Sneftel/gull/frame/rib.scad

// The left-right-perpendicular-ish rib shape, which extends between the two spines on a side and
// supports a fingerboard. Also potentially includes the body of the thumb cluster. 

include <util.scad>
include <params.scad>

// PARAMETERS SPECIFIC TO THIS ASSEMBLY

// The height of the lowest point of the top side of the fingerboard (the fingerboard PCB will go as low as this)
FINGERBOARD_CENTER_HEIGHT = 35;

// The thickness of the fingerboard body
RIB_THICKNESS = 20;

FORWARD_STABILIZER_LOC = 30;

STABILIZER_SEAT_ANGLE = 10;

STABILIZER_SEAT_EXTRA_WIDTH = 1;

LEG_SLOT_DEPTH = 2;
LEG_SLOT_WIDTH = 2;

module LegSlot()
{
    EXTRA = 1;

    pn_neg() {
        translate([-LEG_SLOT_WIDTH/2, -LEG_SLOT_DEPTH, 0])
            square([LEG_SLOT_DEPTH,LEG_SLOT_WIDTH+EXTRA], center=false);
    }
}

module CableSlot()
{
    EXTRA = 1;
    LARGE = 100;
    translate([0, -LEG_SLOT_DEPTH])
        square([LARGE,LEG_SLOT_DEPTH+EXTRA], center=false);
}

module RearwardStabilizerSlot(extraWidth=STABILIZER_SEAT_EXTRA_WIDTH)
{
    EXTRA = 1;
    WIDTH = THICKNESS + extraWidth;

    INNER_DEPTH = STABILIZER_HEIGHT + THICKNESS * tan(STABILIZER_SEAT_ANGLE);
    OUTER_DEPTH = STABILIZER_HEIGHT - extraWidth * tan(STABILIZER_SEAT_ANGLE);

    pn_neg() {
        polygon(points = [
            [-WIDTH + THICKNESS/2, -OUTER_DEPTH],
            [THICKNESS/2, -INNER_DEPTH],
            [THICKNESS/2, EXTRA],
            [-WIDTH + THICKNESS/2, EXTRA]]);
    }

    pn_anchor("stabilizer") children();
}

module ForwardStabilizerSlot()
{
    scale([-1,1,1]) RearwardStabilizerSlot(extraWidth=10) children();
}

module OnArc(radius, x)
{
    RotZ(angleFromLen(radius, x)) translate([0,-radius,0])
        children();
}

module FingerboardPlatform(minorRadius, withTC)
{
    // The length of the rib's fingerboard platform forward of the center of the middle bolt hole
    RIB_FORWARD_EXTENT = 30 + THICKNESS/2 + STABILIZER_SEAT_EXTRA_WIDTH;

    // The length of the rib's fingerboard platform forward of the center of the middle bolt hole
    RIB_REARWARD_EXTENT = FINGERBOARD_REARWARD_EXTENT;


    TOTAL_ANGLE = angleFromLen(minorRadius, RIB_FORWARD_EXTENT+RIB_REARWARD_EXTENT);
    ANGLE_BIAS = angleFromLen(minorRadius, (RIB_FORWARD_EXTENT-RIB_REARWARD_EXTENT)/2);
    
    RotZ(ANGLE_BIAS)
    pn_pos()
        CocktailSausage(minorRadius, TOTAL_ANGLE, RIB_THICKNESS);
        
    OnArc(minorRadius, -20) FingerboardTSlot();
    OnArc(minorRadius, -10) LegSlot();
    OnArc(minorRadius, 0) FingerboardTSlot();
    OnArc(minorRadius, 10) LegSlot();
    OnArc(minorRadius, 20) FingerboardTSlot();

    OnArc(minorRadius, -30) RearwardStabilizerSlot() children();
    OnArc(minorRadius, 30) ForwardStabilizerSlot() children();
    OnArc(minorRadius, 0) pn_anchor("pcb") children();

    OnArc(minorRadius+15, 32+THICKNESS) CableGuide();

    if(withTC) {
        OnArc(minorRadius, -RIB_REARWARD_EXTENT+6) translate([0,-TC_DOWNWARD_SHIFT]) RotZ(-TC_ELEVATION_ANGLE)
        {
            pn_pos() Rect(4*TC_INTERCONNECT_OFFSET, 20, ANCHOR_RT, extraX=5);
            translate([-4*TC_INTERCONNECT_OFFSET,0]) scale([1,-1,1]) Interconnect("TC", offsetLength=TC_INTERCONNECT_OFFSET, horizontalKeepout=0) children();
        }

        //OnArc(minorRadius+12, -40-THICKNESS) RotZ(90) CableGuide();
    }
}

module Supports(shift, minorRadius)
{
    FINGERBOARD_MAJOR_RADIUS = minorRadius + RIB_THICKNESS;
    EXTRA=1;
    LARGE=100;

    pn_pos() {
        difference() {
            Rect(SPINES_OUTER_SPACING, LARGE, ANCHOR_CB);
            translate([shift, minorRadius+FINGERBOARD_CENTER_HEIGHT])
                circle(r=FINGERBOARD_MAJOR_RADIUS-EXTRA);
        }
    }

    translate([SPINES_OUTER_SPACING/2,0]) RotZ(90) Interconnect("foo", SPINE_RIB_INTERCONNECT_OFFSET);
    scale([-1,1,1]) translate([SPINES_OUTER_SPACING/2,0]) RotZ(90) Interconnect("foo", SPINE_RIB_INTERCONNECT_OFFSET);
}

module Rib(shift, minorRadius, cantAngle, withTC)
{
    Supports(shift, minorRadius) children();

    translate([shift,minorRadius+FINGERBOARD_CENTER_HEIGHT]) RotZ(cantAngle)
        FingerboardPlatform(minorRadius, withTC) children();
}


module Rib_Anchored(shift, minorRadius, cantAngle, withTC)
{
    RotZ(90)
    translate([-SPINES_OUTER_SPACING/2+THICKNESS/2, -2*SPINE_RIB_INTERCONNECT_OFFSET])
        Rib(shift, minorRadius, cantAngle, withTC) children();
}

Dekerf() pn_top() Rib_Anchored(RIB_A_SHIFT, RIB_A_RADIUS, RIB_A_PITCH, true);
