Sneftel/gull/frame/rib_c.scad

// The outer-most ribs.

include <params.scad>
use <rib.scad>

module Rib_C()
{
	Rib_Anchored(RIB_C_SHIFT, RIB_C_RADIUS, RIB_C_PITCH, false) children();
}

Dekerf() pn_top() Rib_C();
